laura-regan/Bitcoiner-Expansion-Board/Bitcoiner-Expansion-Board/3D models/ABL.STEP

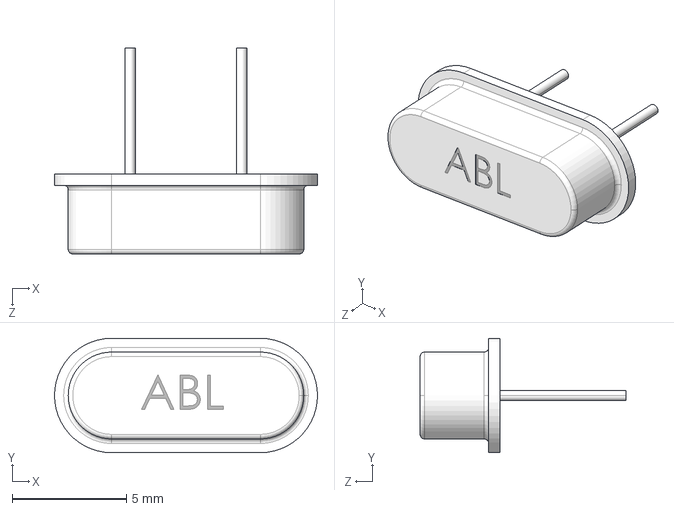
[picture p20: CAD file, 2021-08-03]
Bitcoiner-Expansion-Board/3D models/ABL.STEP
11.5 x 5.00 x 9.00 mm
