laura-regan/Bitcoiner-Expansion-Board/Bitcoiner-Expansion-Board/3D models/T491A475K016AT.step

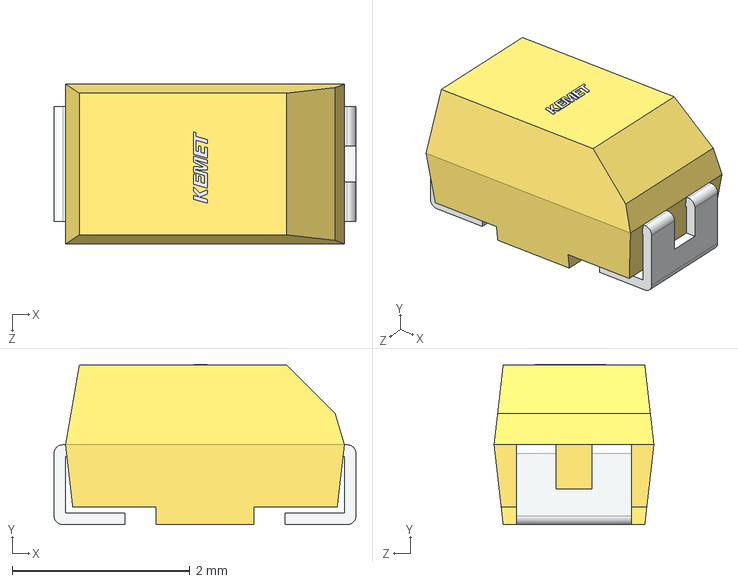
[picture p21: CAD file, 2021-08-03]
Bitcoiner-Expansion-Board/3D models/T491A475K016AT.step
3.40 x 1.81 x 1.80 mm
