laura-regan/Bitcoiner-Expansion-Board/Bitcoiner-Expansion-Board/3D models/vls6045ex.step

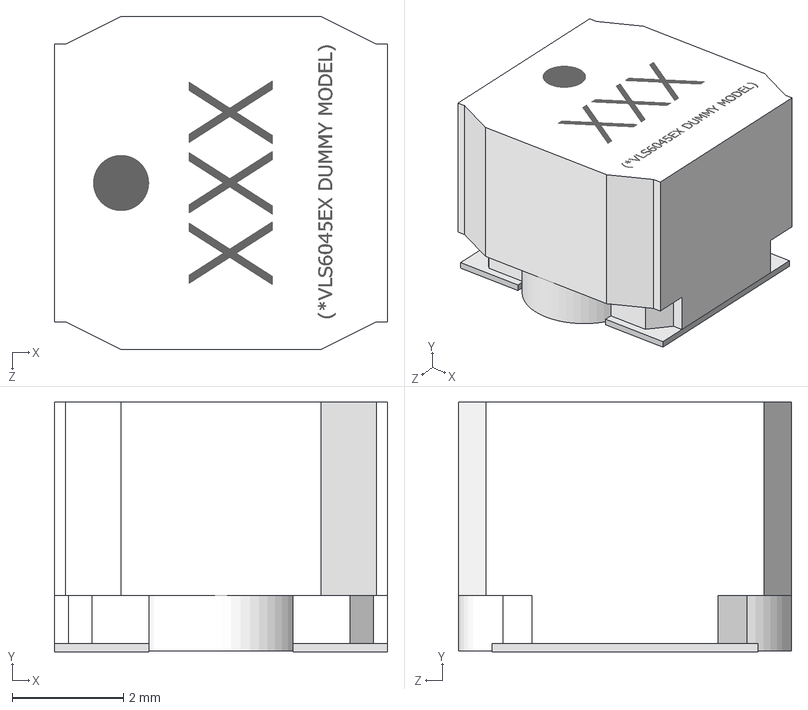
[picture p22: CAD file, 2021-08-03]
Bitcoiner-Expansion-Board/3D models/vls6045ex.step
6.00 x 4.50 x 6.00 mm
VLS6045EX_C(3Dmodel)
VLS6045EX_T(3Dmodel)
