laura-regan/Bitcoiner-Expansion-Board/Bitcoiner-Expansion-Board/3D models/SSW-106-02-T-D-RA.stp

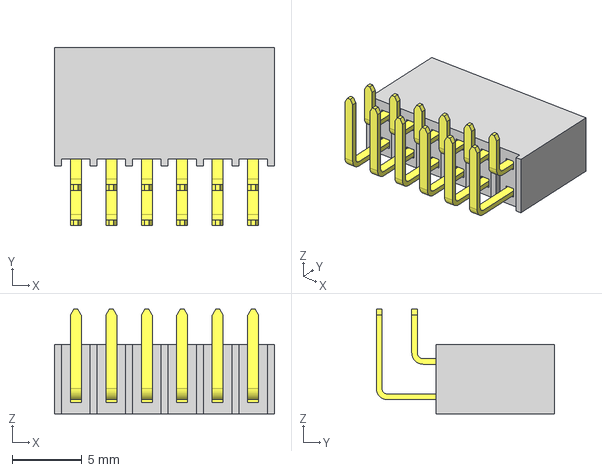
[picture p23: CAD file, 2021-08-03]
Bitcoiner-Expansion-Board/3D models/SSW-106-02-T-D-RA.stp
15.7 x 12.8 x 7.48 mm
_T1SSW-106-02-T-D-RA
_P2SSW-106-02-T-D-RA
