laura-regan/Bitcoiner-Expansion-Board/Bitcoiner-Expansion-Board/3D models/LTD-2601G.step

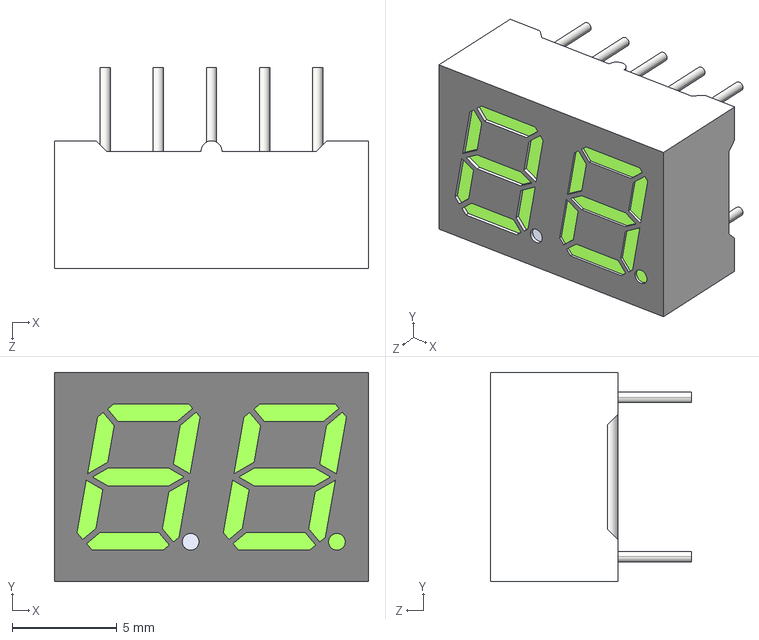
[picture p24: CAD file, 2021-08-03]
Bitcoiner-Expansion-Board/3D models/LTD-2601G.step
15.0 x 10.0 x 9.60 mm
Pins
