laura-regan/Bitcoiner-Expansion-Board/Bitcoiner-Expansion-Board/3D models/DPAK.step

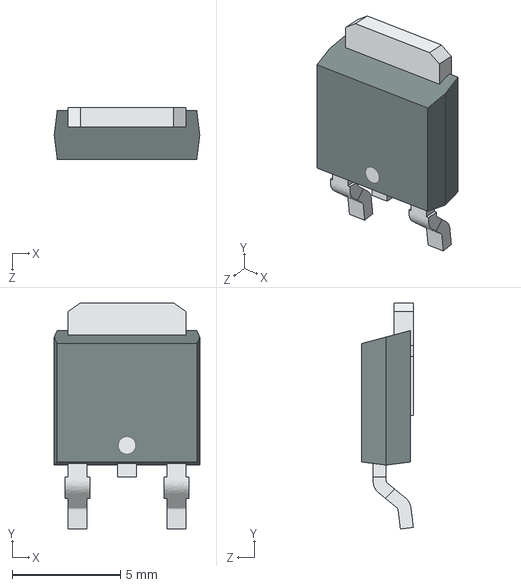
[picture p25: CAD file, 2021-08-03]
Bitcoiner-Expansion-Board/3D models/DPAK.step
6.73 x 10.4 x 2.39 mm
