laura-regan/Bitcoiner-Expansion-Board/Bitcoiner-Expansion-Board/3D models/vls6045ex-h.step

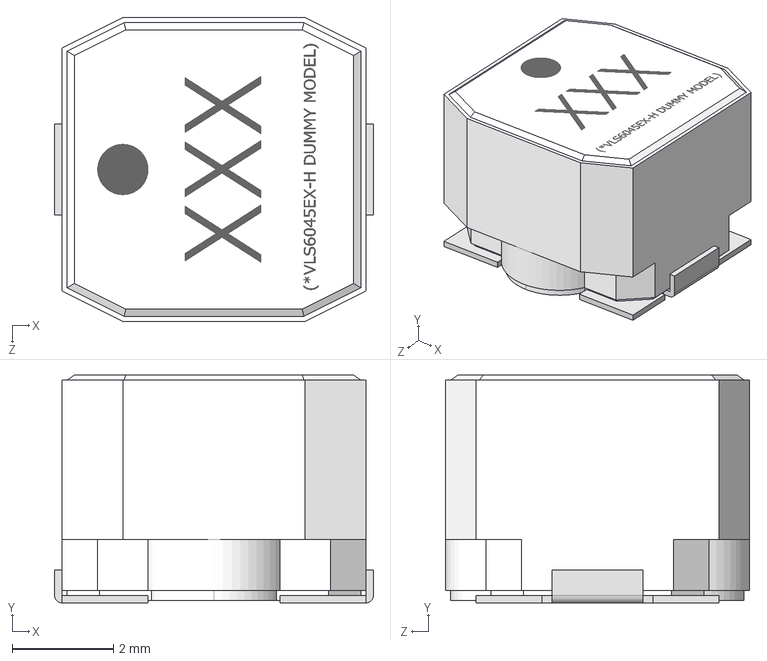
[picture p26: CAD file, 2021-08-03]
Bitcoiner-Expansion-Board/3D models/vls6045ex-h.step
6.30 x 4.50 x 6.00 mm
VLS6045EX-H_C(3Dmodel)
VLS6045EX-H_T(3Dmodel)
