laura-regan/Bitcoiner-Expansion-Board/Bitcoiner-Expansion-Board/3D models/DO-219AB.stp

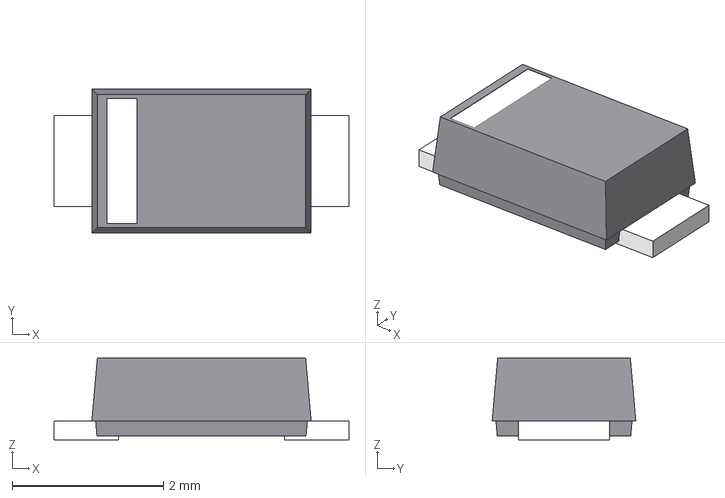
[picture p27: CAD file, 2021-08-03]
Bitcoiner-Expansion-Board/3D models/DO-219AB.stp
3.90 x 1.90 x 1.08 mm
