laura-regan/Bitcoiner-Expansion-Board/Bitcoiner-Expansion-Board/3D models/CAPC2012X94N EIA 0805.step

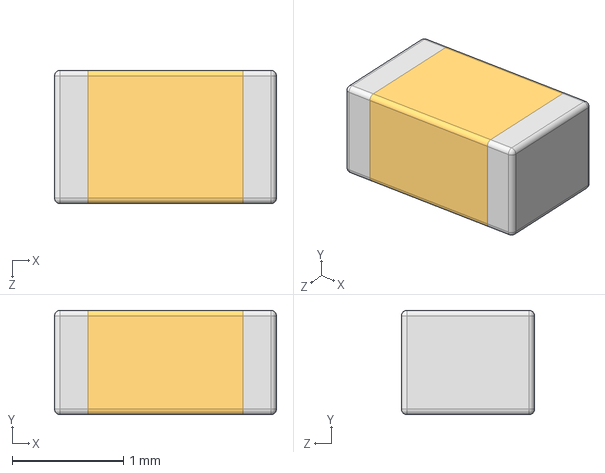
[picture p28: CAD file, 2021-08-03]
Bitcoiner-Expansion-Board/3D models/CAPC2012X94N EIA 0805.step
2.00 x 0.94 x 1.20 mm
