laura-regan/Bitcoiner-Expansion-Board/Bitcoiner-Expansion-Board/3D models/SOT-23-6.step

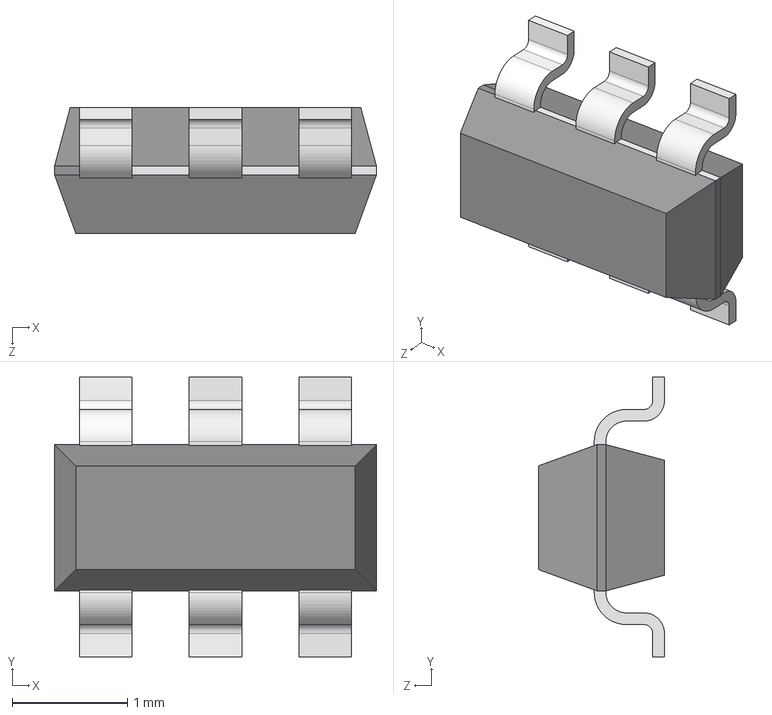
[picture p29: CAD file, 2021-08-03]
Bitcoiner-Expansion-Board/3D models/SOT-23-6.step
2.79 x 2.43 x 1.09 mm
