laura-regan/Bitcoiner-Expansion-Board/Bitcoiner-Expansion-Board/3D models/SQT-110-01-F-D-RA.stp

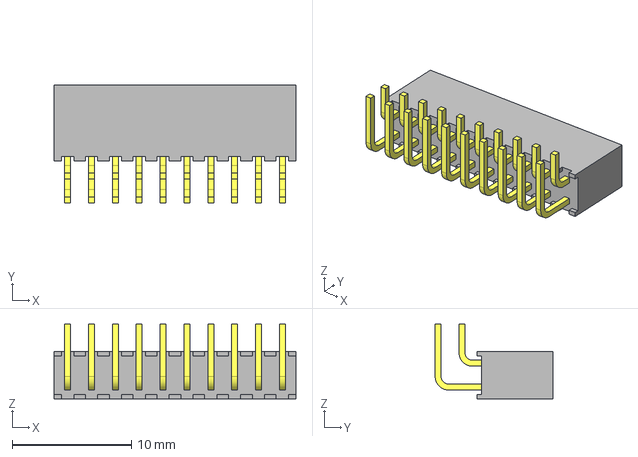
[picture p30: CAD file, 2021-08-03]
Bitcoiner-Expansion-Board/3D models/SQT-110-01-F-D-RA.stp
20.3 x 9.87 x 6.29 mm
_S1SQT-110-01-F-D-RA
_P1SQT-110-01-F-D-RA
