laura-regan/Bitcoiner-Expansion-Board/Bitcoiner-Expansion-Board/3D models/Inductor SMD 7850.stp

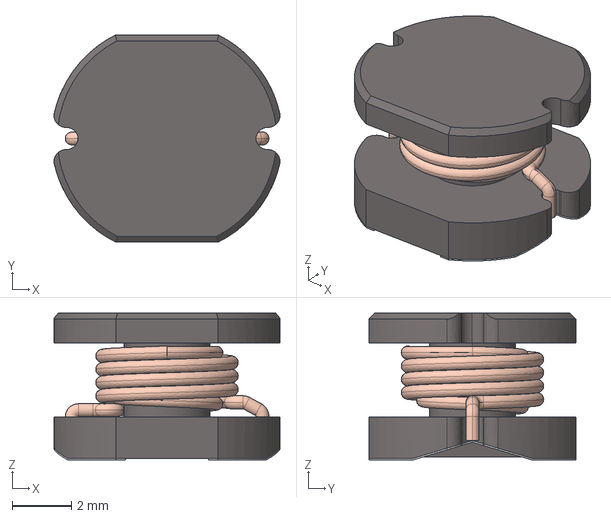
[picture p31: CAD file, 2021-08-03]
Bitcoiner-Expansion-Board/3D models/Inductor SMD 7850.stp
7.63 x 7.00 x 4.95 mm
