laura-regan/Bitcoiner-Expansion-Board/Bitcoiner-Expansion-Board/3D models/TSW-105-05-G-S.stp

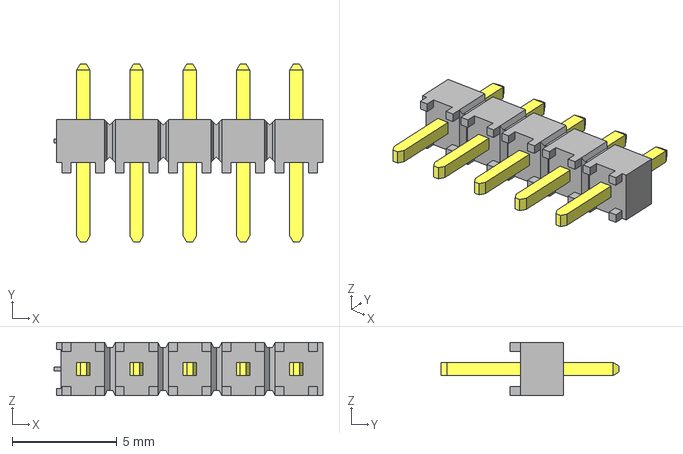
[picture p32: CAD file, 2021-08-03]
Bitcoiner-Expansion-Board/3D models/TSW-105-05-G-S.stp
12.8 x 8.51 x 2.54 mm
_TSW-105-05-G-S_body
_T-1S6-21-TSW-1-05-5-S
