laura-regan/Bitcoiner-Expansion-Board/Bitcoiner-Expansion-Board/3D models/HEADER_3PINS_2.54MM.STEP

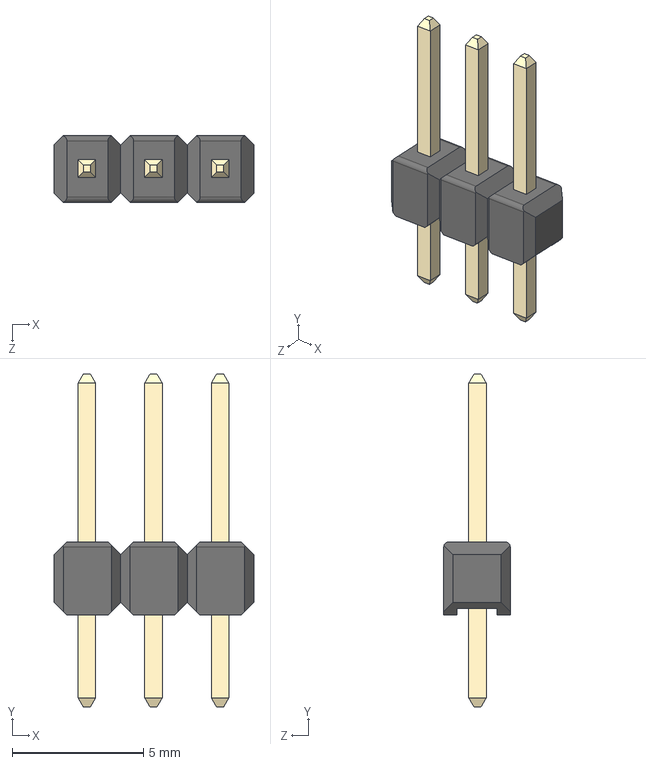
[picture p33: CAD file, 2021-08-03]
Bitcoiner-Expansion-Board/3D models/HEADER_3PINS_2.54MM.STEP
7.62 x 12.7 x 2.54 mm
holder
pin x 3
