laura-regan/Bitcoiner-Expansion-Board/Bitcoiner-Expansion-Board/3D models/fuse_silicon_0603L.step

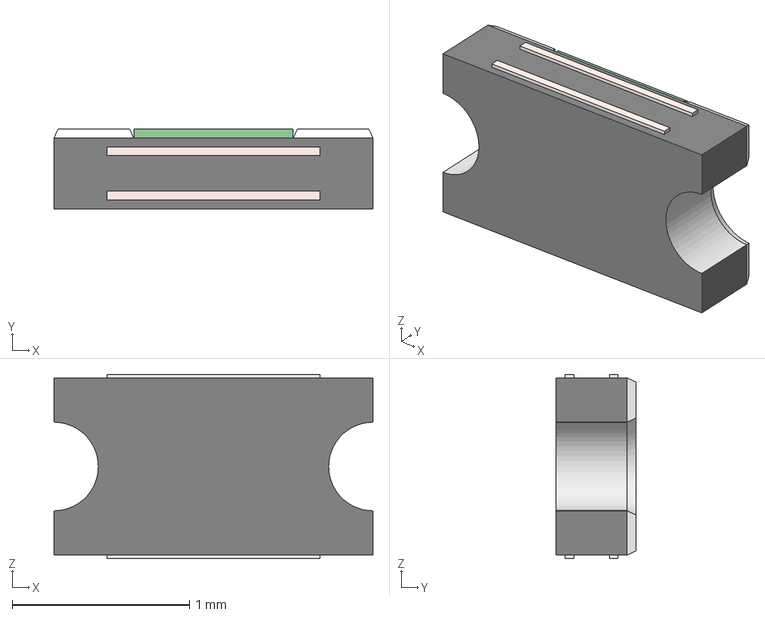
[picture p34: CAD file, 2021-08-03]
Bitcoiner-Expansion-Board/3D models/fuse_silicon_0603L.step
1.80 x 0.45 x 1.04 mm
