laura-regan/Bitcoiner-Expansion-Board/Bitcoiner-Expansion-Board/3D models/SOT353-1.step

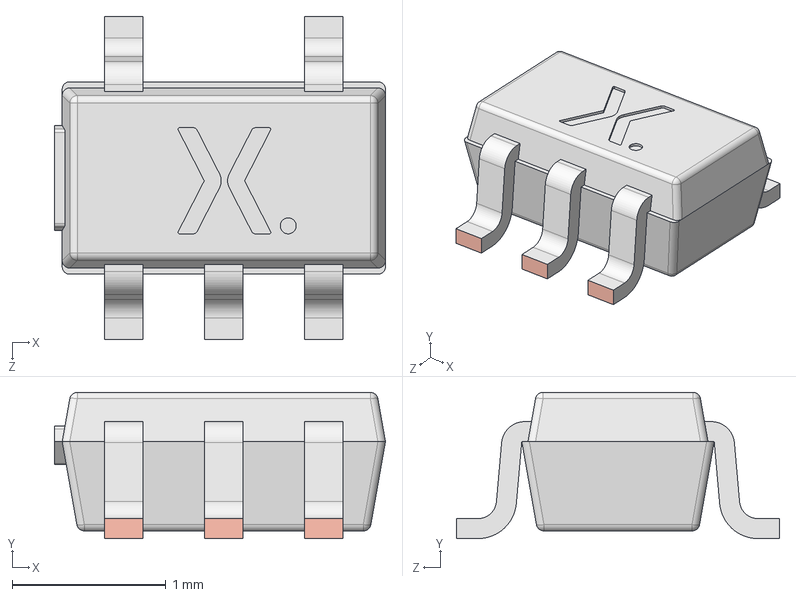
[picture p35: CAD file, 2021-08-03]
Bitcoiner-Expansion-Board/3D models/SOT353-1.step
2.15 x 0.95 x 2.10 mm
SOT353-1 Lower body
SOT353-1 Lead x 5
SOT353-1 Upper body
