laura-regan/Bitcoiner-Expansion-Board/Bitcoiner-Expansion-Board/3D models/EDH106M025A9BAA.step

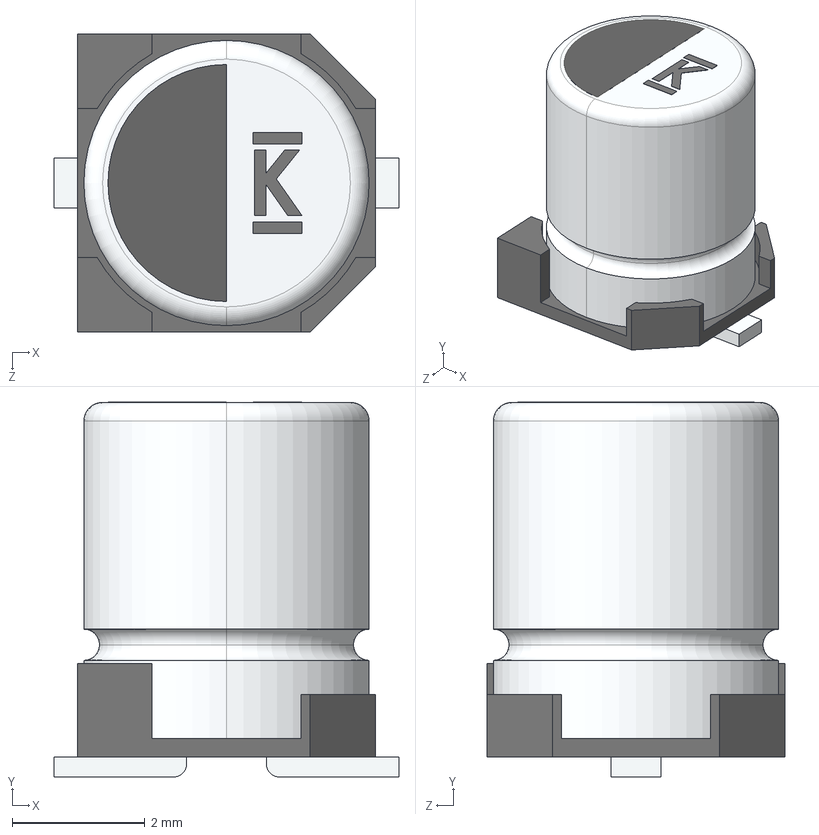
[picture p36: CAD file, 2021-08-03]
Bitcoiner-Expansion-Board/3D models/EDH106M025A9BAA.step
5.20 x 5.66 x 4.50 mm
