laura-regan/Bitcoiner-Expansion-Board/Bitcoiner-Expansion-Board/3D models/lqfp64.step

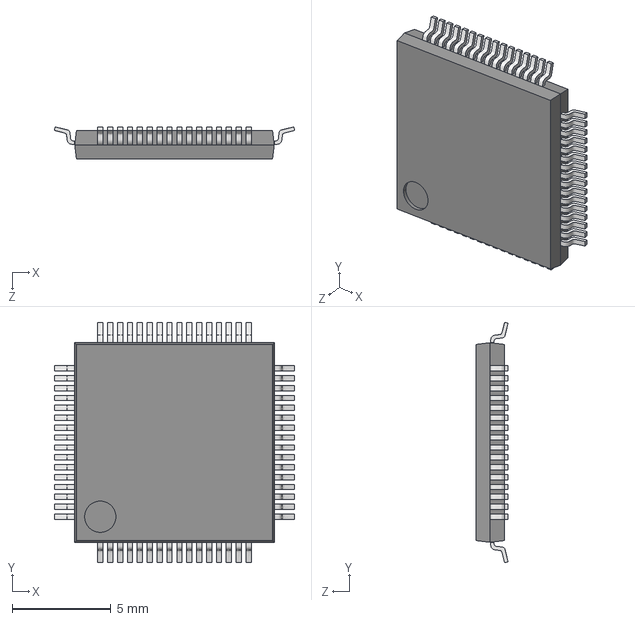
[picture p37: CAD file, 2021-08-03]
Bitcoiner-Expansion-Board/3D models/lqfp64.step
12.1 x 12.1 x 1.63 mm
