laura-regan/Bitcoiner-Expansion-Board/Bitcoiner-Expansion-Board/3D models/403A-03.STEP

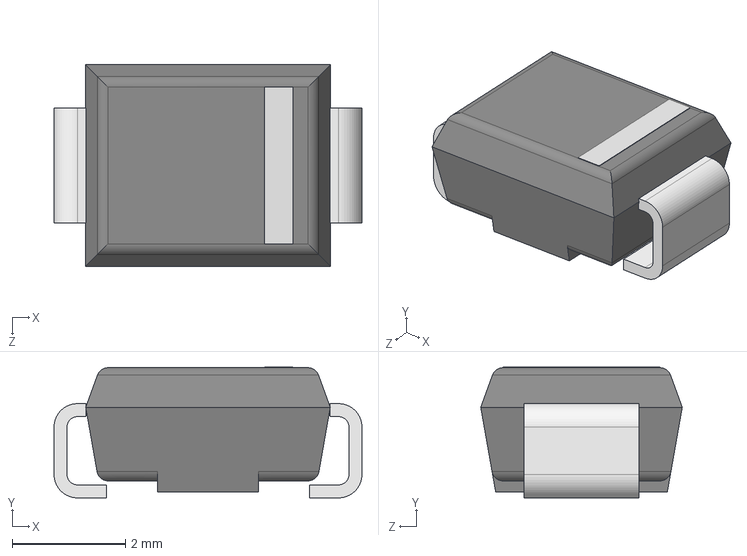
[picture p38: CAD file, 2021-08-03]
Bitcoiner-Expansion-Board/3D models/403A-03.STEP
5.44 x 2.31 x 3.56 mm
